hide63414/HowToMakeBarcoder/Barcodes/Barcode-C_A3+.png

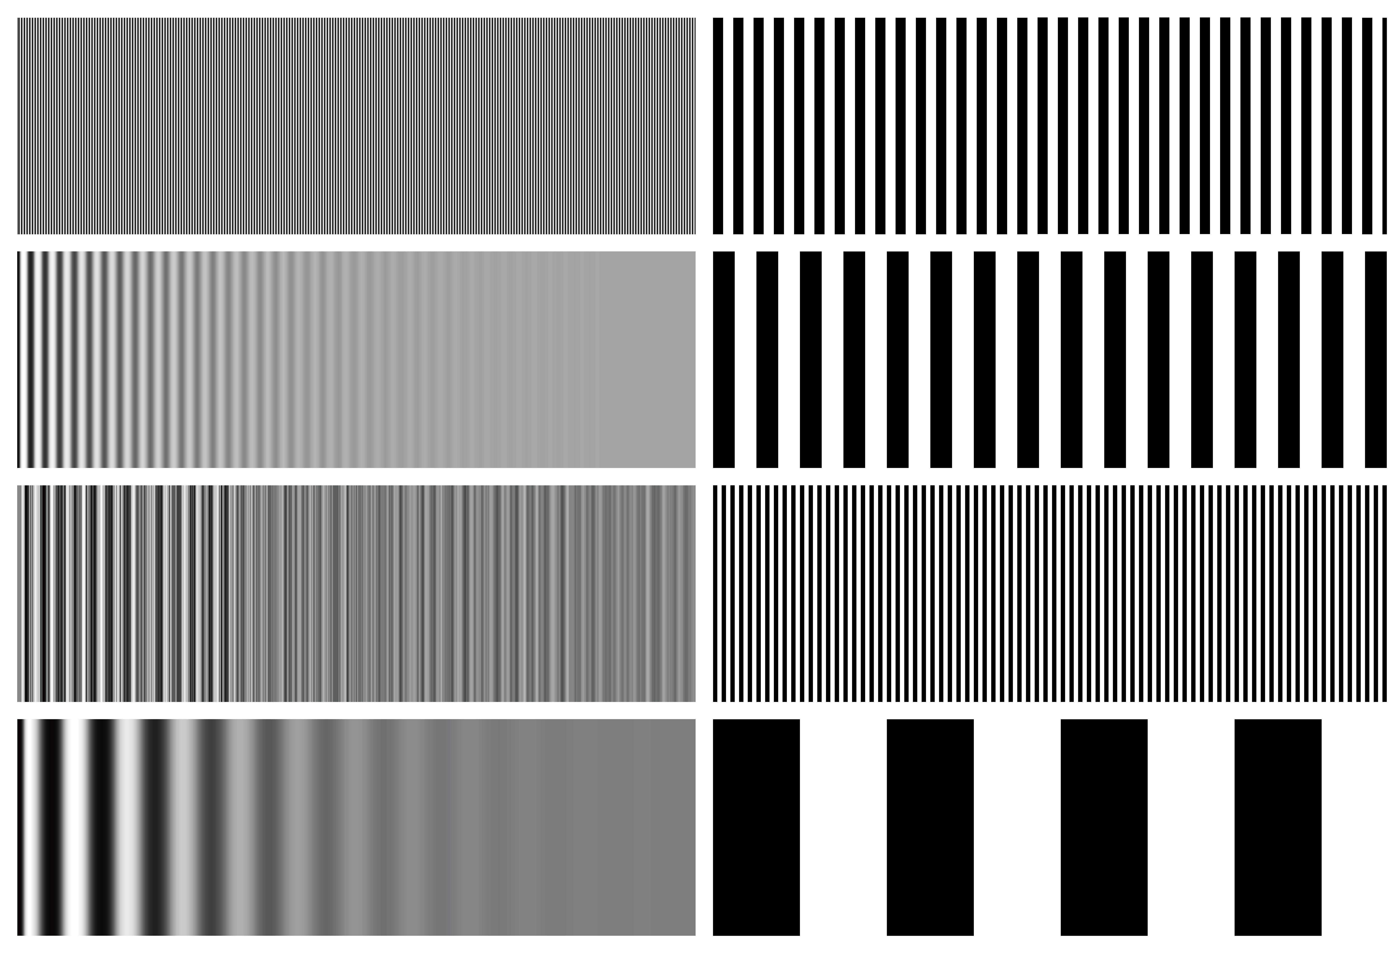
Barcodes/Barcode-C_A3+.png
