hide63414/HowToMakeBarcoder/Barcodes/Barcode-D_A3+.png

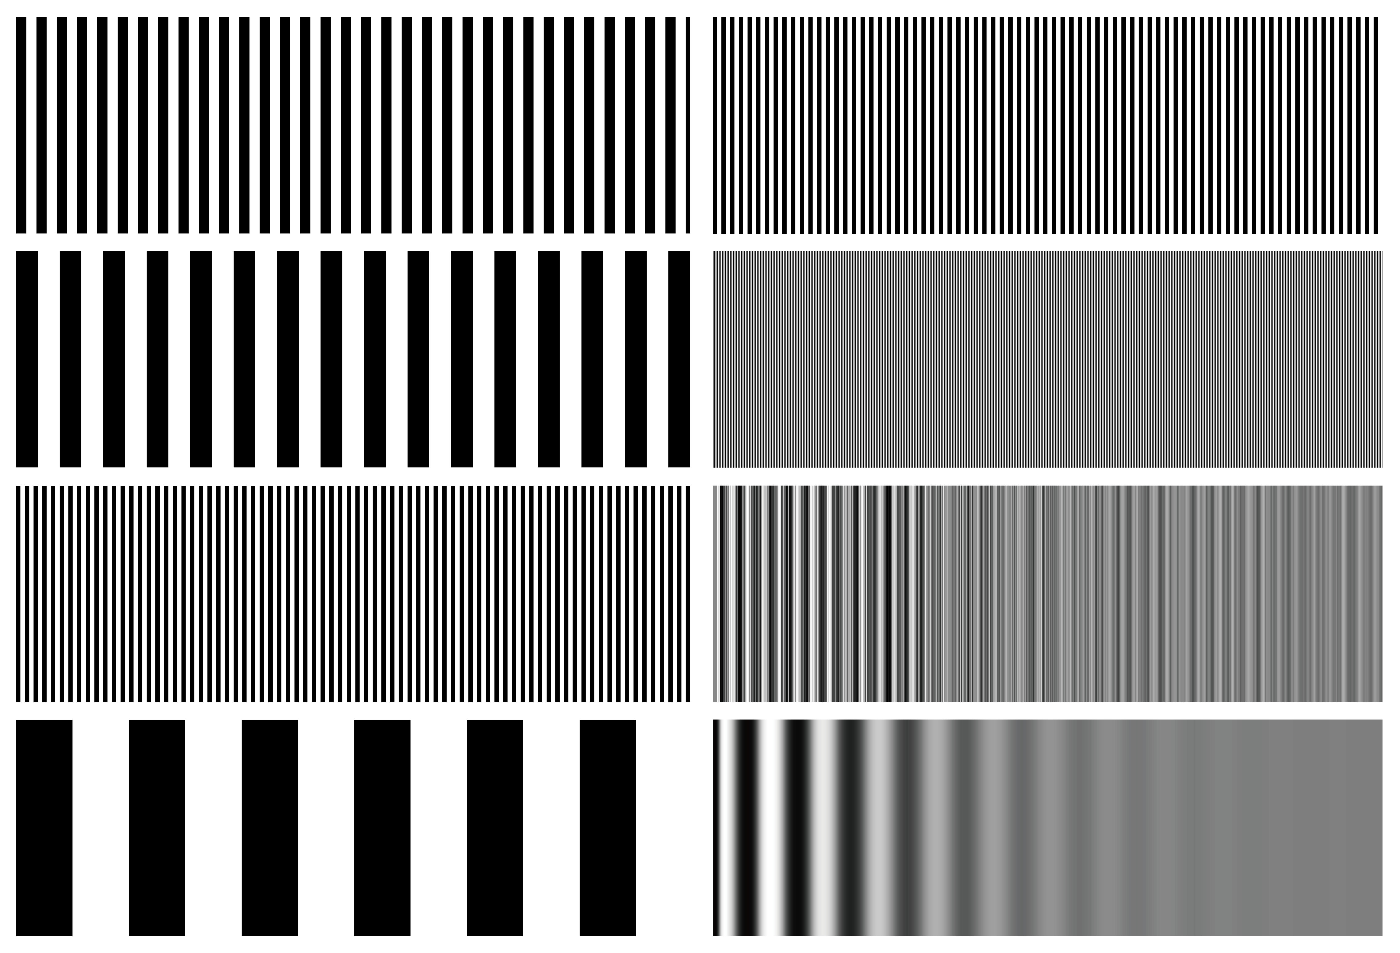
Barcodes/Barcode-D_A3+.png
