hide63414/HowToMakeBarcoder/Barcodes/Barcodes-A_A3+.png

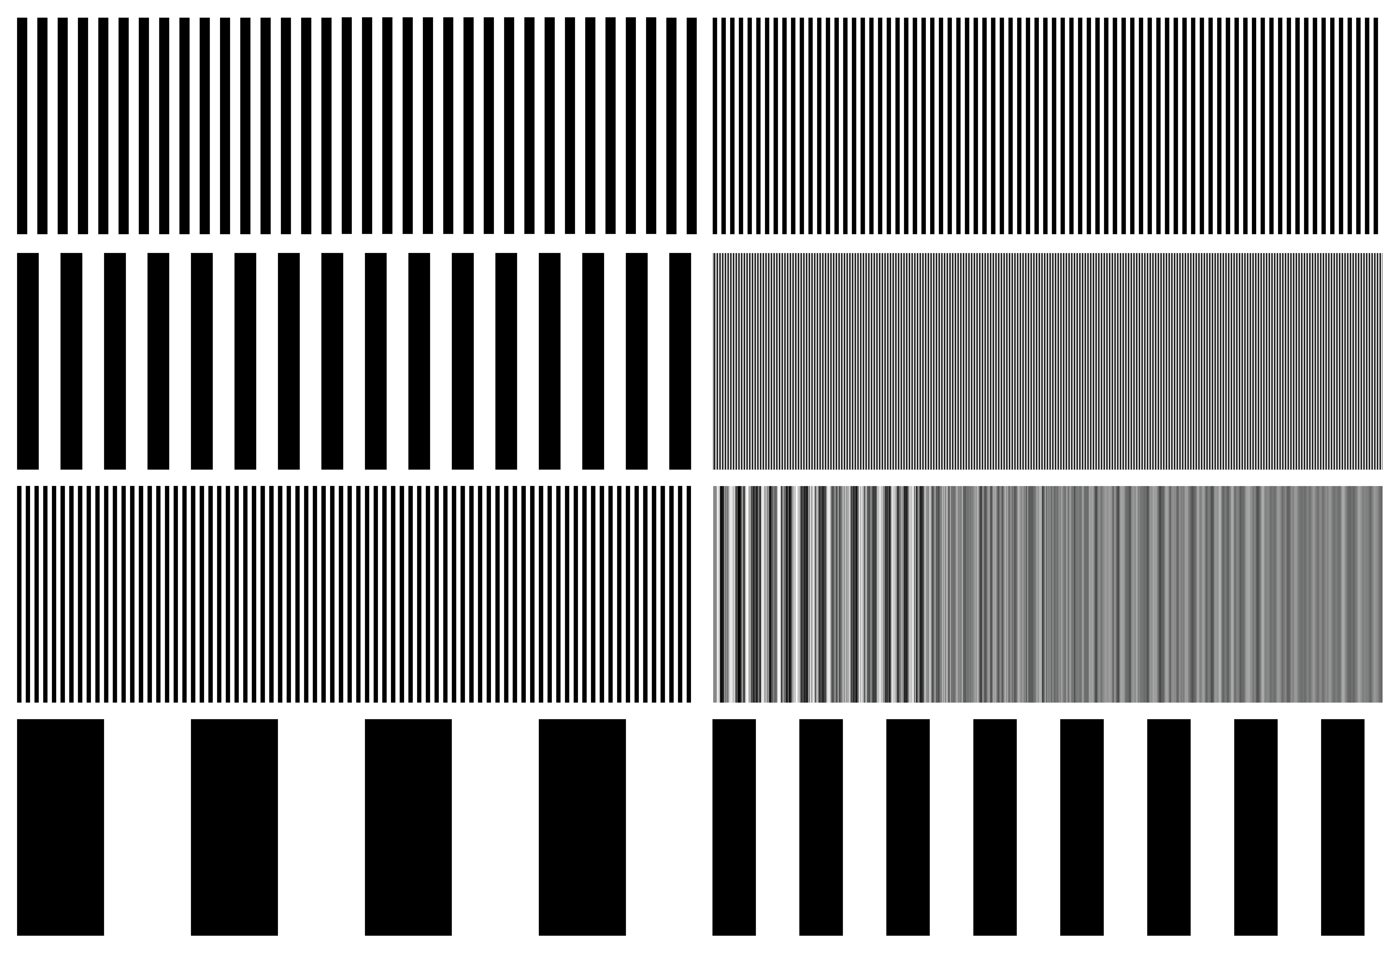
Barcodes/Barcodes-A_A3+.png
