hide63414/HowToMakeBarcoder/Barcodes/Barcodes-B_A3+.png

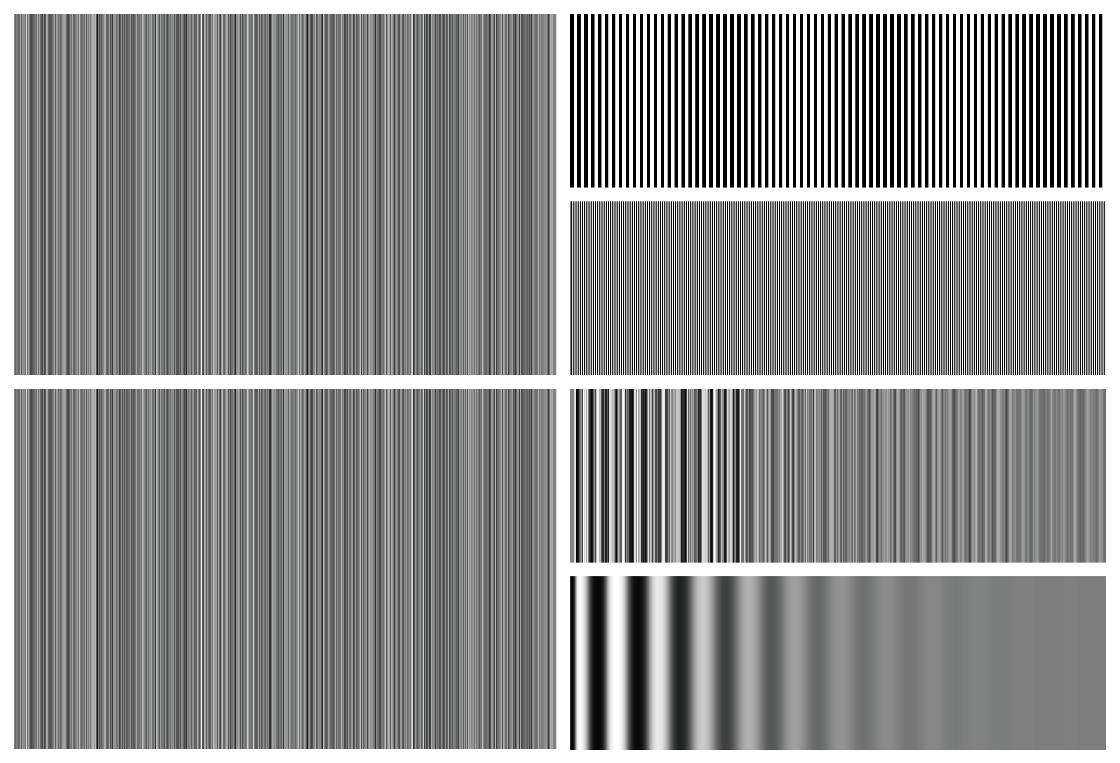
Barcodes/Barcodes-B_A3+.png
