hide63414/HowToMakeBarcoder/Barcodes/Barcodes-E_A3+.png

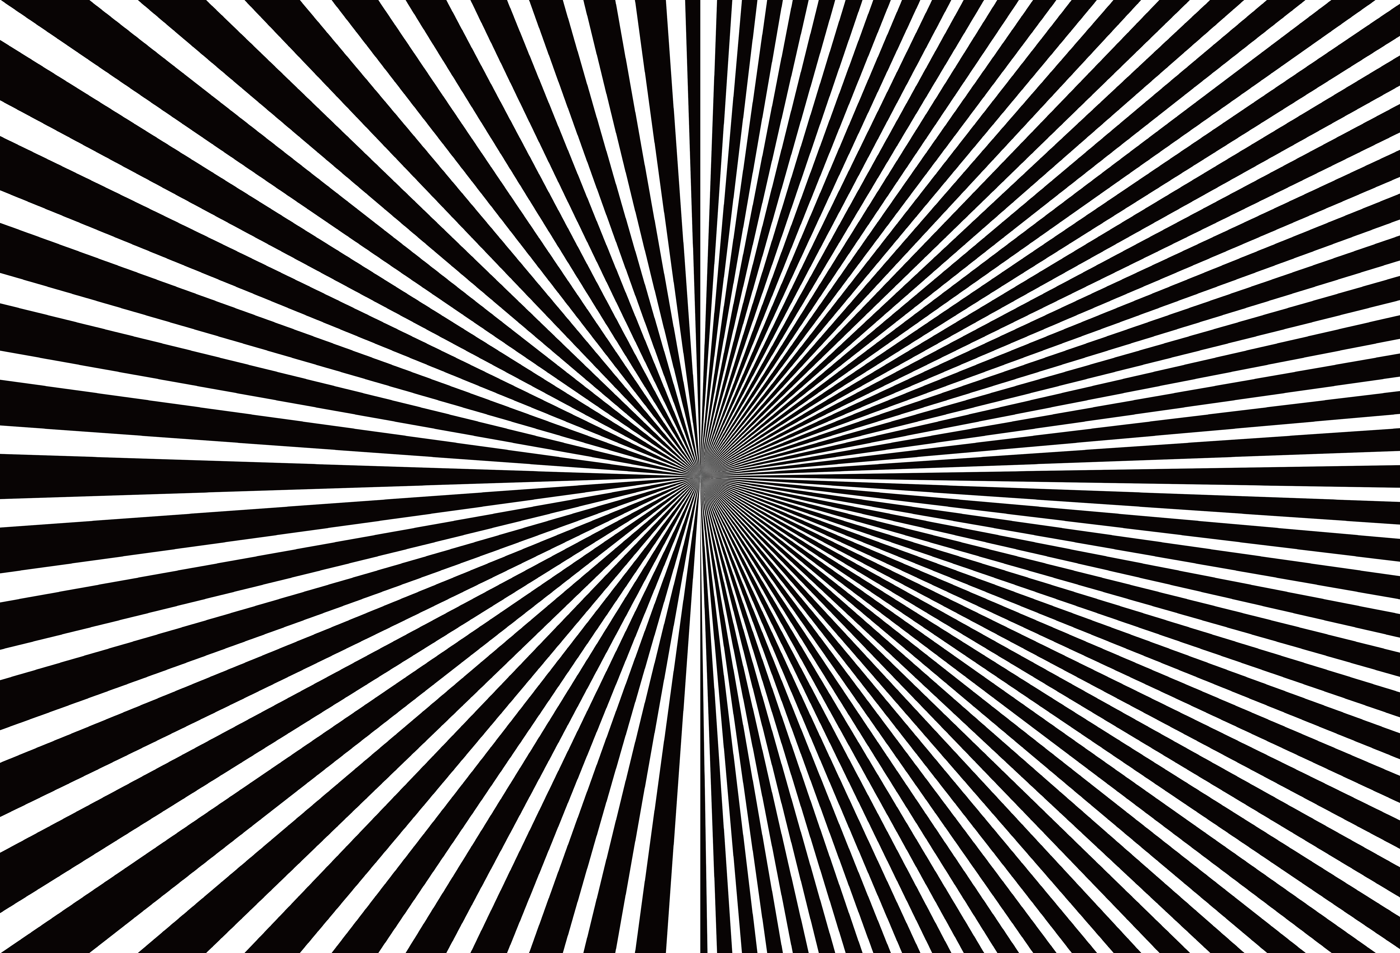
Barcodes/Barcodes-E_A3+.png
