hide63414/HowToMakeBarcoder/Barcodes/DOREMI_A4.png

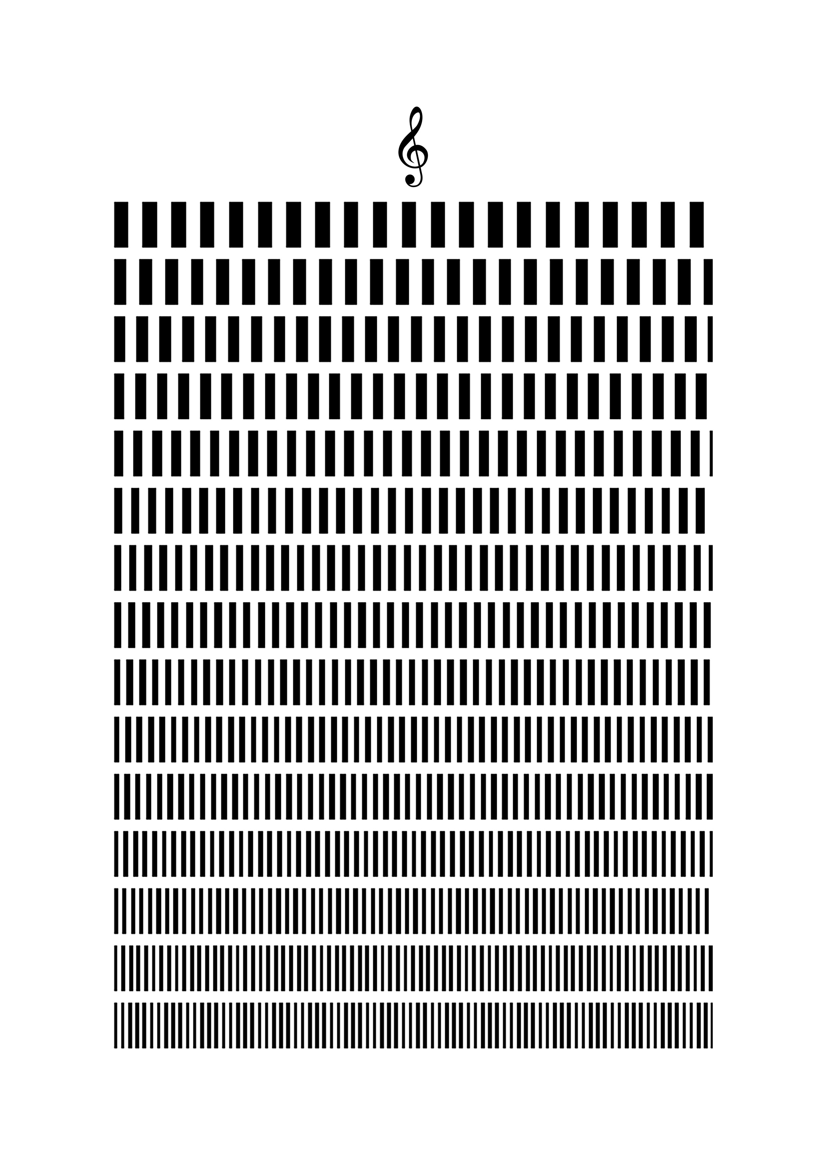
Barcodes/DOREMI_A4.png
