hide63414/HowToMakeBarcoder/Barcodes/HappyBirthBarcoday_A4.png

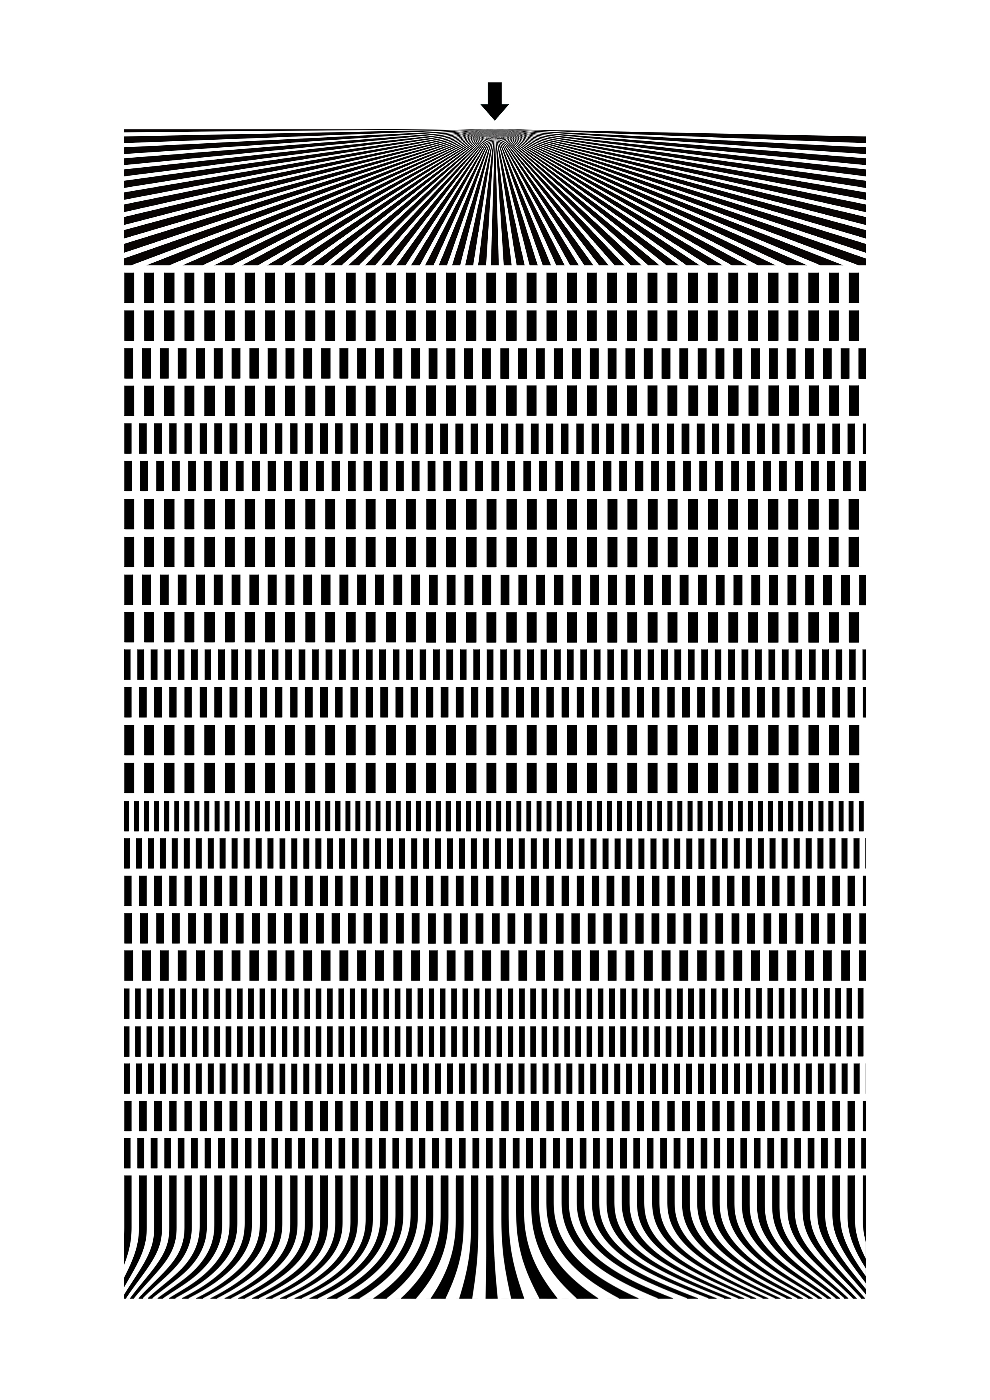
Barcodes/HappyBirthBarcoday_A4.png
