hide63414/HowToMakeBarcoder/Barcodes/Hello.png

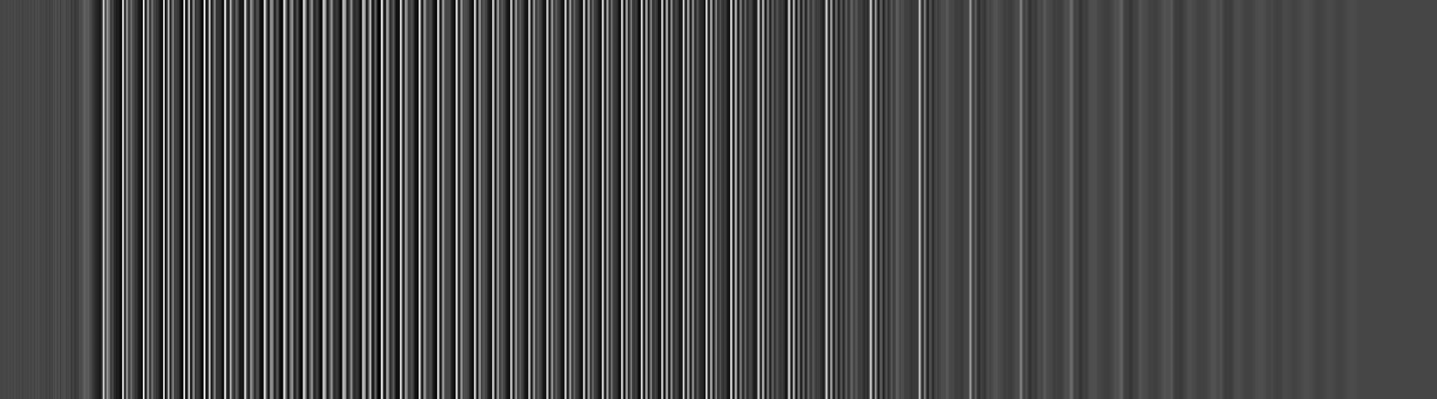
Barcodes/Hello.png
