hide63414/HowToMakeBarcoder/Barcodes/ILoveYou.png

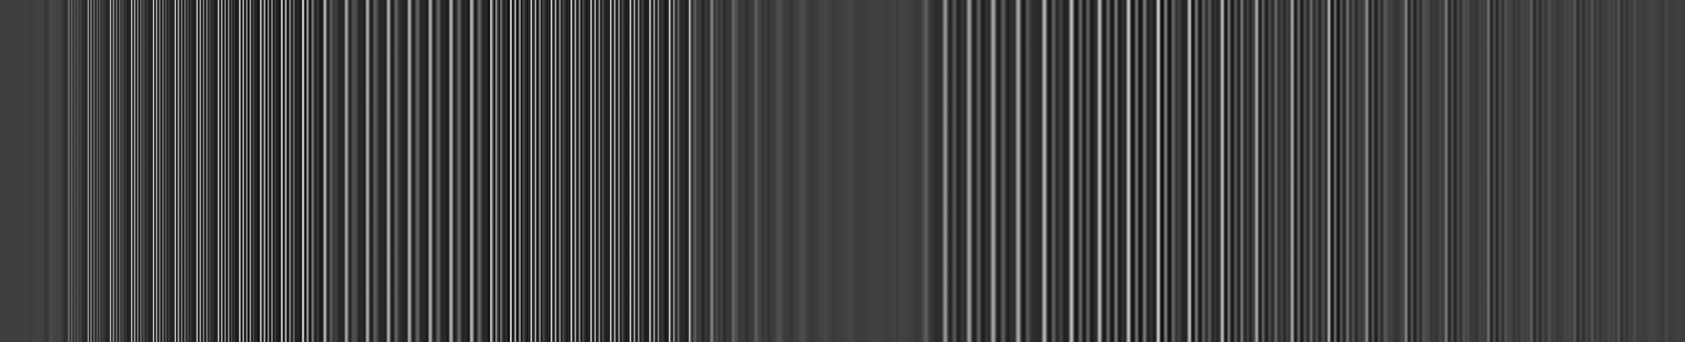
Barcodes/ILoveYou.png
